gdex1974/AirSensorInternalESP32/main/GroupBitView.h

#pragma once

#include <freertos/FreeRTOS.h>
#include <freertos/event_groups.h>

class GroupBitView
{
public:
#if __GNUC__ >= 8
    using EventGroupHandleType = EventGroupHandle_t;
#else
    using EventGroupHandleType = void*;
#endif

    GroupBitView() = default;
    GroupBitView(EventGroupHandleType group, int bit) : group(group), bit(bit) {}
    EventGroupHandleType getGroup() const { return group; }
    bool wait(int timeoutMs) const
    {
        return (xEventGroupWaitBits(getGroup(), bit, pdFALSE, pdFALSE, timeoutMs / portTICK_PERIOD_MS) & bit) != 0;
    }
    bool waitClear(int timeoutMs) const
    {
        return (xEventGroupWaitBits(getGroup(), bit, pdTRUE, pdFALSE, timeoutMs / portTICK_PERIOD_MS) & bit) != 0;
    }
    bool wait() const
    {
        return wait(portMAX_DELAY);
    }
    bool waitClear() const
    {
        return waitClear(portMAX_DELAY);
    }
    void set() const
{
        xEventGroupSetBits(getGroup(), bit);
    }

    void clear() const
    {
        xEventGroupClearBits(getGroup(), bit);
    }
private:
    EventGroupHandleType group = nullptr;
    EventBits_t bit = 0;
};
