gdex1974/AirSensorInternalESP32/main/SPS30DataProvider.h

#pragma once

#include "SPS30/Sps30Uart.h"

class SPS30DataProvider
{
public:
    explicit SPS30DataProvider(embedded::PacketUart& packetUart)
    : sps30(packetUart)
    {
    }

    bool setup(bool wakeUp);
    bool startMeasure();
    bool wakeUp();

    bool sleep()
    {
        return sps30.sleep() == embedded::Sps30Error::Success;
    }

    bool hibernate();
    bool getMeasureData(int& pm1, int& pm25, int& pm10);
private:
    embedded::Sps30Uart sps30;
};
